Sillybutts/Alchemist/STLs Alchemist 3-7-2024/STLs1_Main/Green/Grip_Left.stl

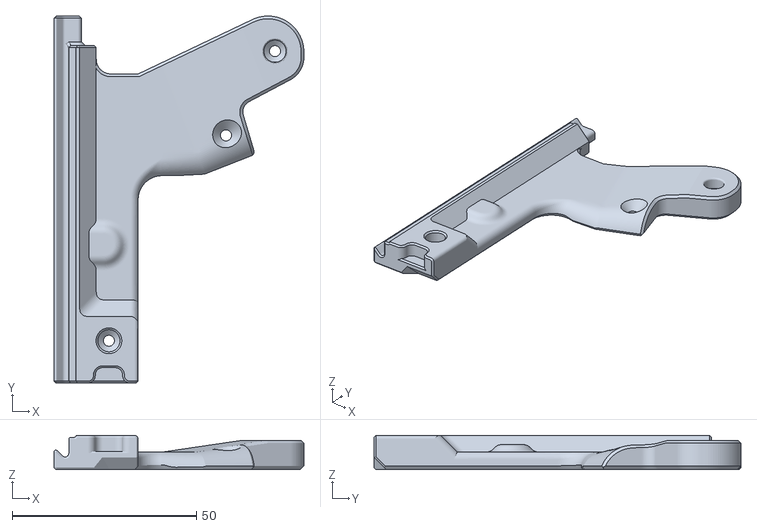
[picture p39: CAD file, 2024-03-08]
STLs Alchemist 3-7-2024/STLs1_Main/Green/Grip_Left.stl
67.8 x 99.5 x 9.25
