Sillybutts/Alchemist/STLs Alchemist 3-7-2024/STLs1_Main/Orange/Sear March2024Update.stl

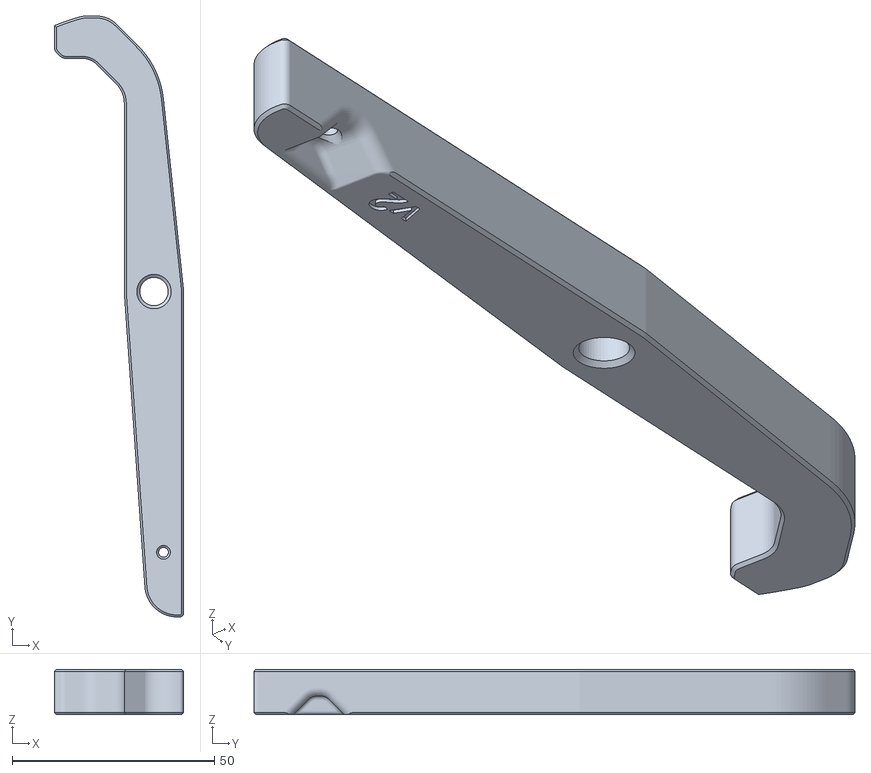
[picture p40: CAD file, 2024-03-08]
STLs Alchemist 3-7-2024/STLs1_Main/Orange/Sear March2024Update.stl
32.0 x 148.7 x 11.2
