Sillybutts/Alchemist/STLs Alchemist 3-7-2024/STLs1_Main/Stocks/Skeggox Stock/Skeggox_Bottom.stl

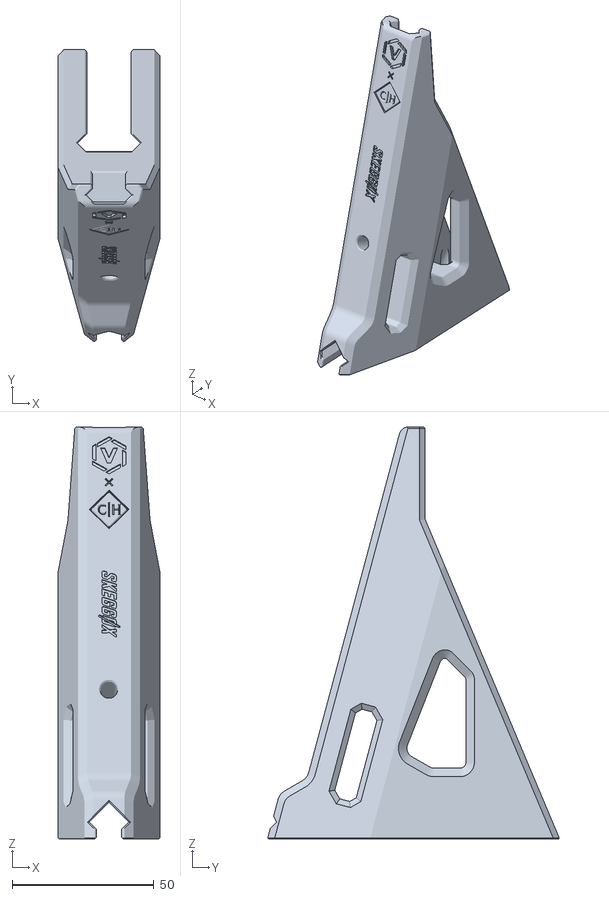
[picture p42: CAD file, 2024-03-08]
STLs Alchemist 3-7-2024/STLs1_Main/Stocks/Skeggox Stock/Skeggox_Bottom.stl
36.0 x 103.0 x 145.6
