Sillybutts/Alchemist/STLs Alchemist 3-7-2024/STLs1_Main/Stocks/Worker-SBL Stock/SBLWRKRSTOCK_Latch.stl

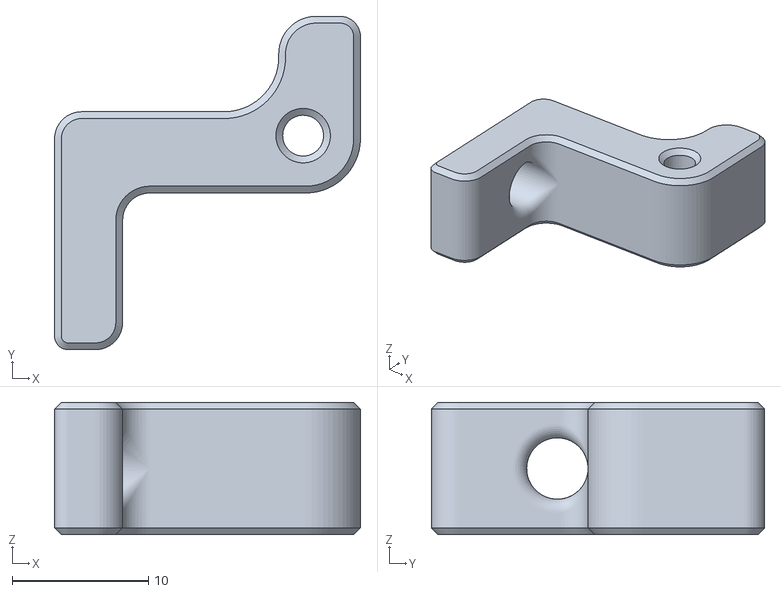
[picture p43: CAD file, 2023-09-10]
STLs Alchemist 3-7-2024/STLs1_Main/Stocks/Worker-SBL Stock/SBLWRKRSTOCK_Latch.stl
22.4 x 24.5 x 9.70
