Sillybutts/Alchemist/STLs Alchemist 3-7-2024/STLs2_Extras/Extras/Lynx Grip/Lynx_GripRight.stl

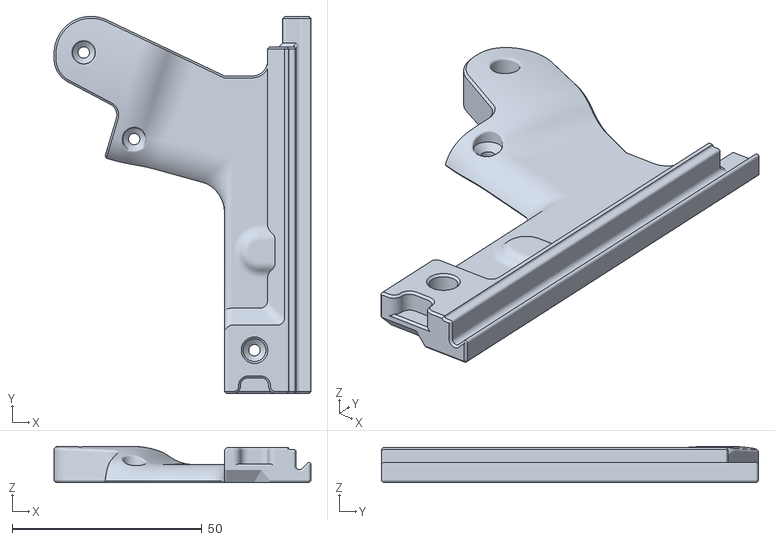
[picture p44: CAD file, 2024-03-08]
STLs Alchemist 3-7-2024/STLs2_Extras/Extras/Lynx Grip/Lynx_GripRight.stl
67.8 x 99.5 x 9.52
