Sillybutts/Alchemist/STLs Alchemist 3-7-2024/STLs2_Extras/Extras/SpigotSCAR/SpigotSCAR_BarrelCap.stl

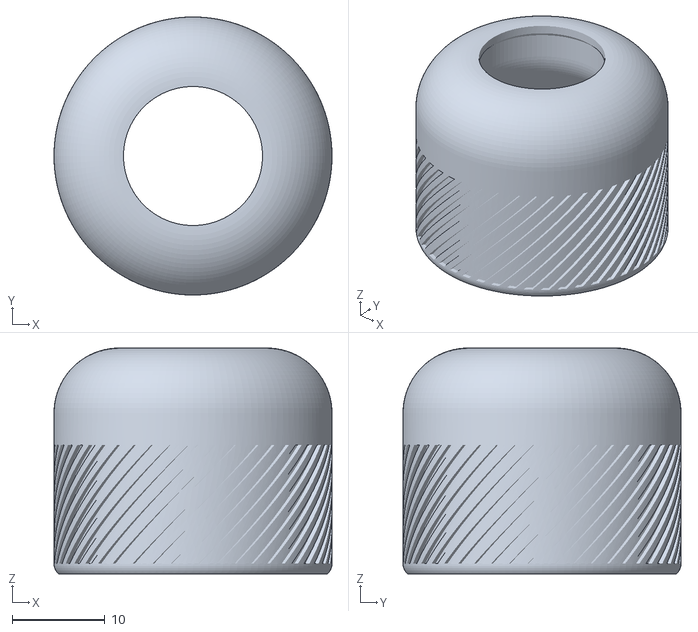
[picture p45: CAD file, 2023-09-10]
STLs Alchemist 3-7-2024/STLs2_Extras/Extras/SpigotSCAR/SpigotSCAR_BarrelCap.stl
30.0 x 30.0 x 24.4
