Sillybutts/Alchemist/STLs Alchemist 3-7-2024/STLs1_Main/Black/Alternate plunger rods/PlungerRod_TroubleshootingFix March2024Update.stl

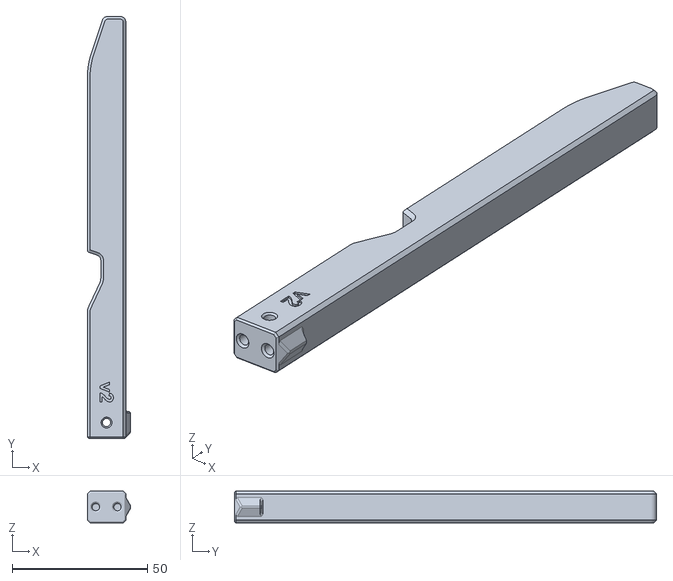
[picture p46: CAD file, 2024-03-08]
STLs Alchemist 3-7-2024/STLs1_Main/Black/Alternate plunger rods/PlungerRod_TroubleshootingFix March2024Update.stl
16.1 x 156.2 x 11.7
