Sillybutts/Alchemist/STLs Alchemist 3-7-2024/STLs1_Main/Black/Rail_C_Smooth.stl

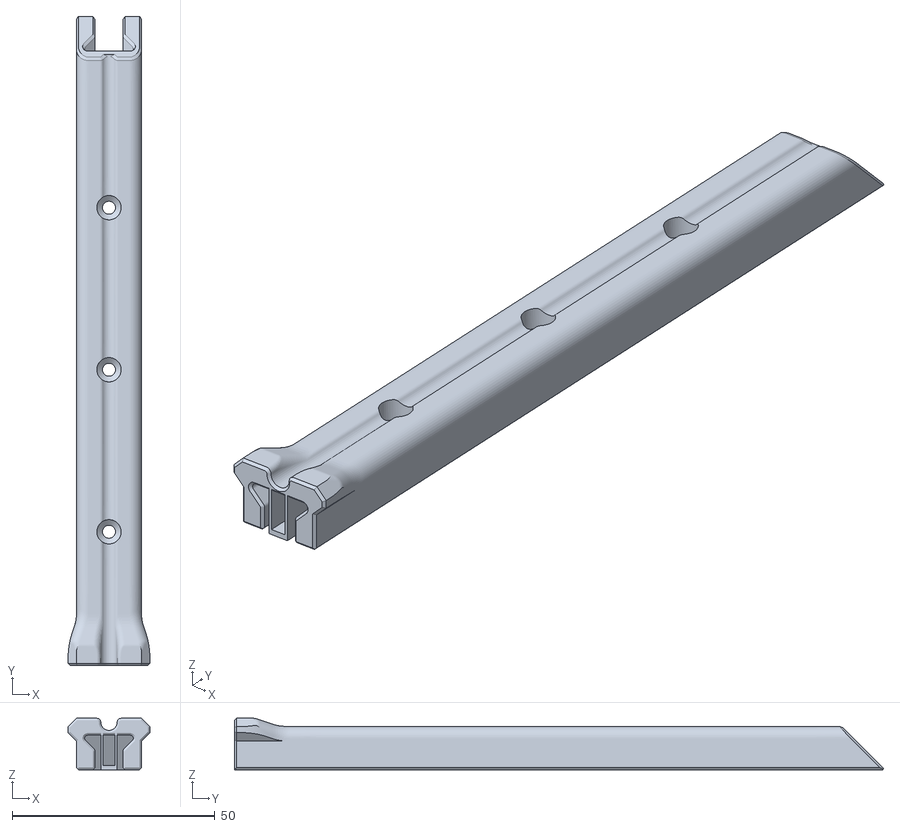
[picture p47: CAD file, 2024-03-08]
STLs Alchemist 3-7-2024/STLs1_Main/Black/Rail_C_Smooth.stl
20.2 x 160.2 x 12.7
