Sillybutts/Alchemist/STLs Alchemist 3-7-2024/STLs1_Main/Orange/PicKeeperTighter.stl

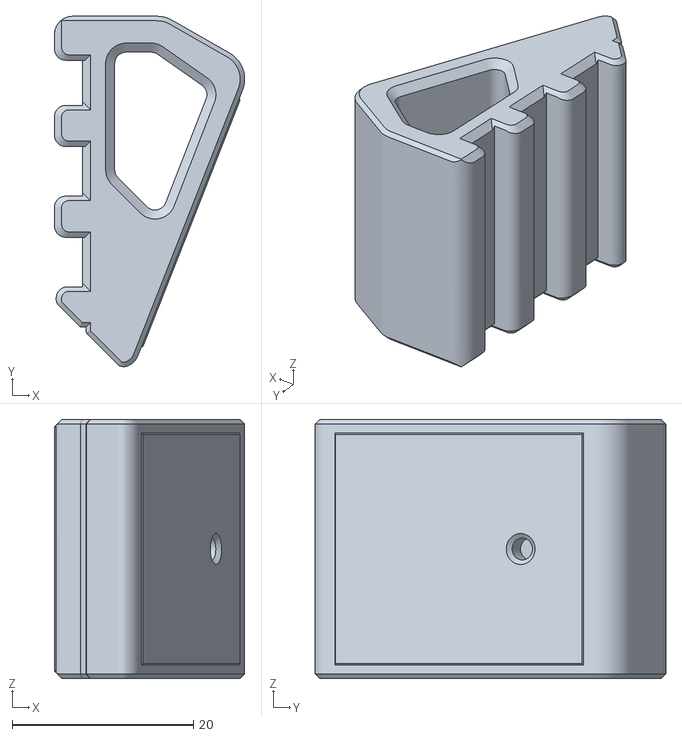
[picture p48: CAD file, 2024-03-08]
STLs Alchemist 3-7-2024/STLs1_Main/Orange/PicKeeperTighter.stl
21.0 x 38.7 x 28.6
