Sillybutts/Alchemist/STLs Alchemist 3-7-2024/STLs1_Main/Stocks/Fixed Stock/FixedStock_Stock.stl

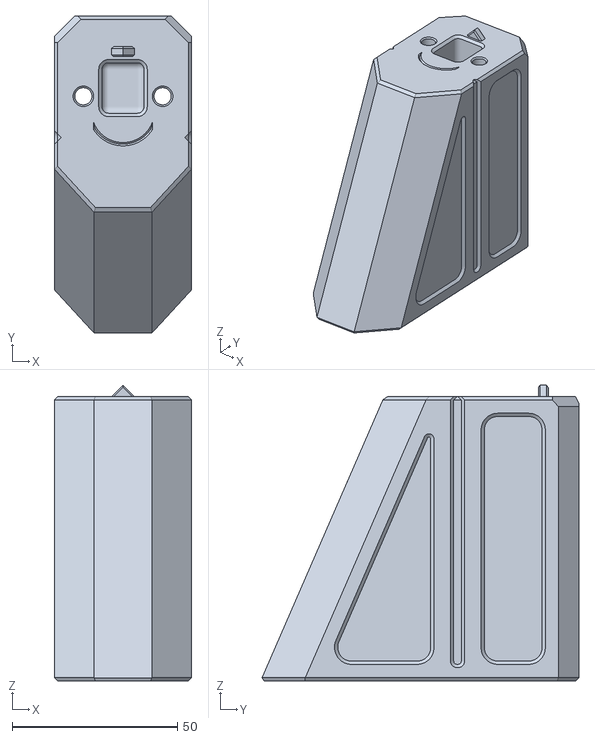
[picture p49: CAD file, 2023-09-10]
STLs Alchemist 3-7-2024/STLs1_Main/Stocks/Fixed Stock/FixedStock_Stock.stl
41.6 x 96.0 x 89.5
