Sillybutts/Alchemist/STLs Alchemist 3-7-2024/STLs1_Main/Stocks/Worker-SBL Stock/SBL_Buttplate.stl

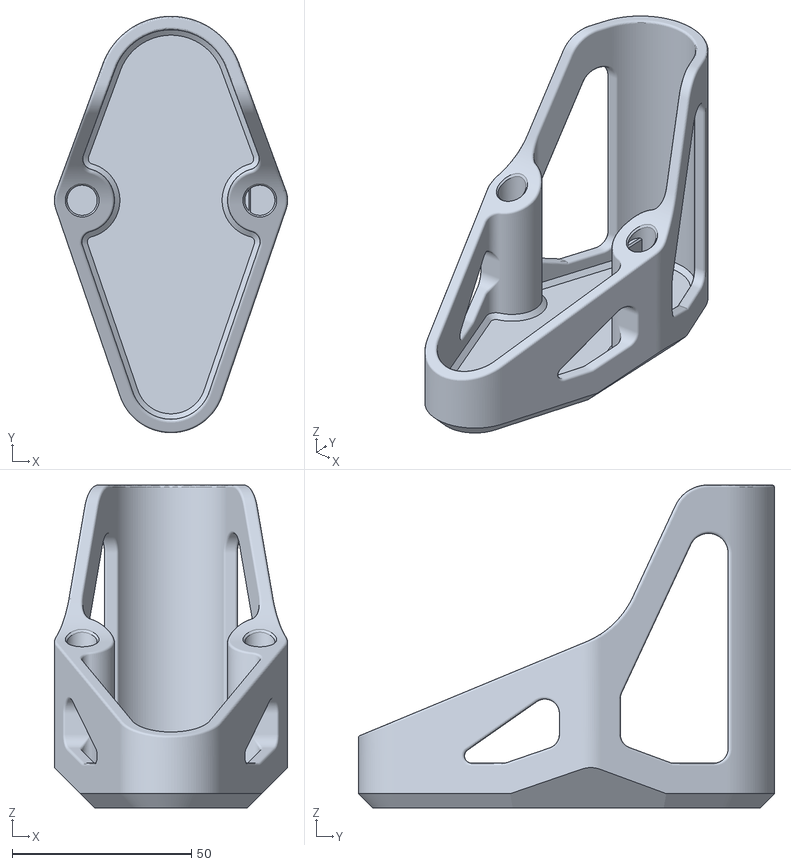
[picture p51: CAD file, 2023-09-10]
STLs Alchemist 3-7-2024/STLs1_Main/Stocks/Worker-SBL Stock/SBL_Buttplate.stl
65.0 x 116.0 x 90.0
