Sillybutts/Alchemist/STLs Alchemist 3-7-2024/STLs2_Extras/Extras/Lynx Grip/Lynx_GripBody_WithShoe.stl

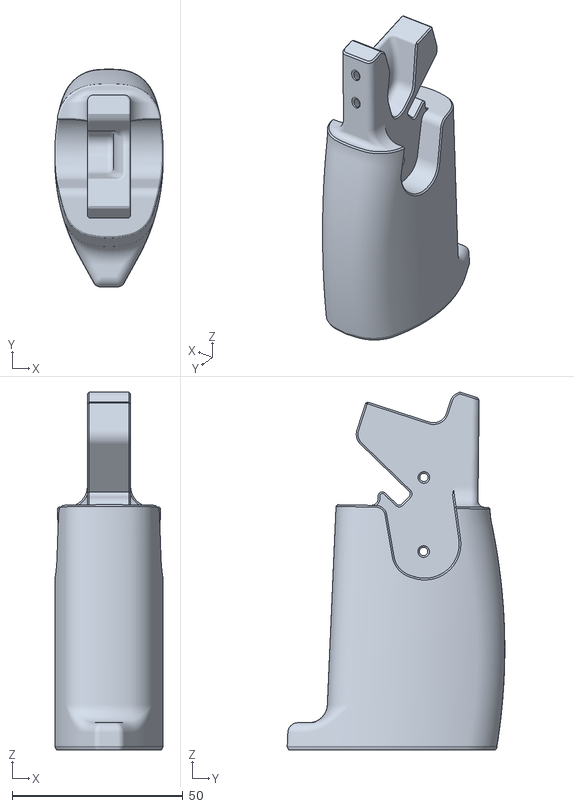
[picture p52: CAD file, 2024-03-08]
STLs Alchemist 3-7-2024/STLs2_Extras/Extras/Lynx Grip/Lynx_GripBody_WithShoe.stl
31.7 x 63.8 x 104.9
