Sillybutts/Alchemist/STLs Alchemist 3-7-2024/STLs2_Extras/Extras/Mag Release with more Trigger Guard space/SmallerArm_MagRelease.stl

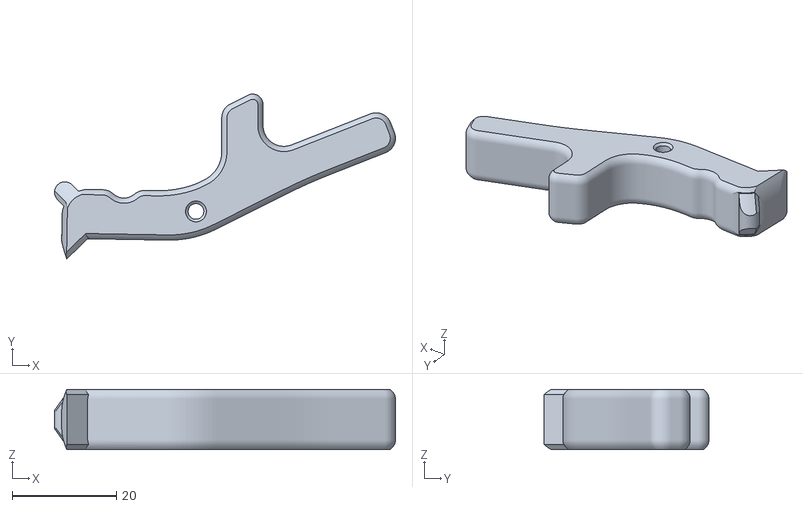
[picture p53: CAD file, 2023-09-10]
STLs Alchemist 3-7-2024/STLs2_Extras/Extras/Mag Release with more Trigger Guard space/SmallerArm_MagRelease.stl
65.4 x 31.6 x 11.5
