Sillybutts/Alchemist/STLs Alchemist 3-7-2024/STLs2_Extras/Extras/PicKeeper original looseness parts/original FrontGrip.stl

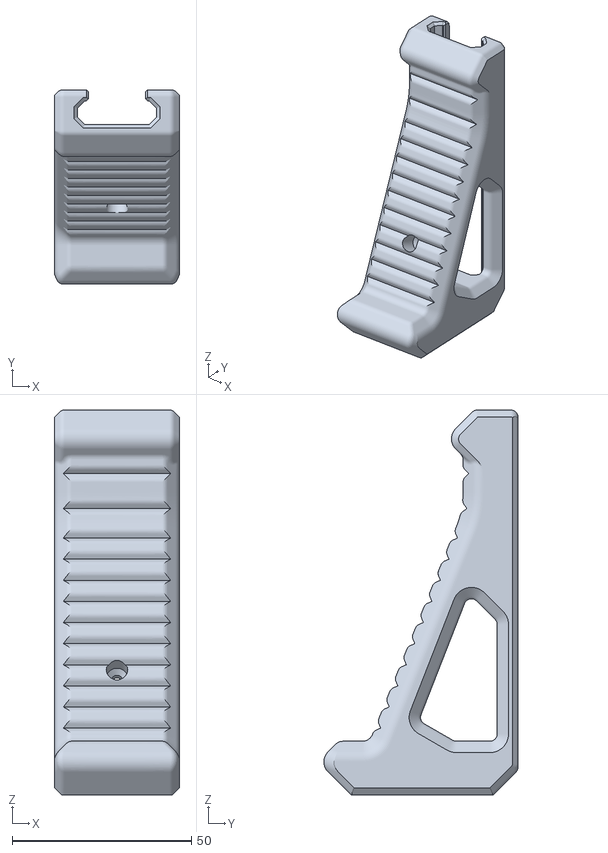
[picture p54: CAD file, 2024-03-08]
STLs Alchemist 3-7-2024/STLs2_Extras/Extras/PicKeeper original looseness parts/original FrontGrip.stl
34.9 x 54.2 x 107.4
