Sillybutts/Alchemist/STLs Alchemist 3-7-2024/STLs2_Extras/Extras/Tools/PT length gauge.stl

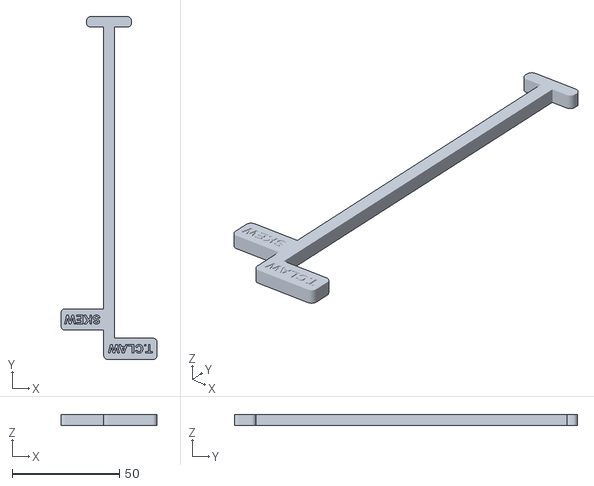
[picture p55: CAD file, 2023-09-10]
STLs Alchemist 3-7-2024/STLs2_Extras/Extras/Tools/PT length gauge.stl
45.0 x 160.3 x 5.00
