Sillybutts/Alchemist/STLs Alchemist 3-7-2024/STLs1_Main/Black/Rail_A.stl

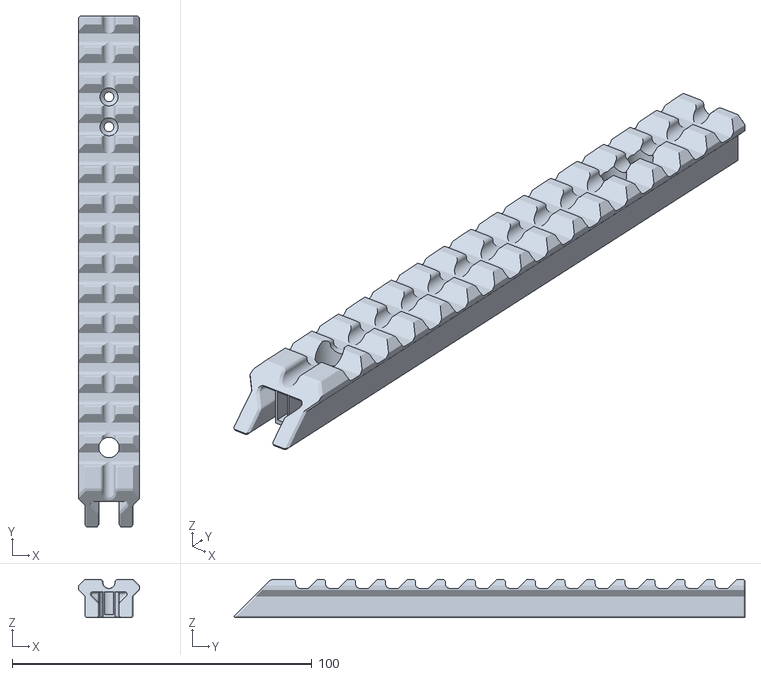
[picture p56: CAD file, 2024-03-08]
STLs Alchemist 3-7-2024/STLs1_Main/Black/Rail_A.stl
20.2 x 170.6 x 12.7
