Sillybutts/Alchemist/STLs Alchemist 3-7-2024/STLs1_Main/Green/MagwellBack.stl

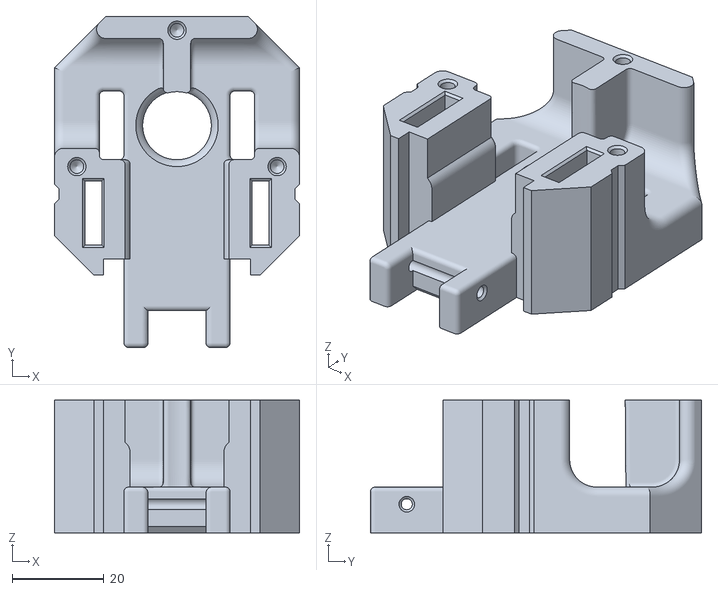
[picture p57: CAD file, 2024-03-08]
STLs Alchemist 3-7-2024/STLs1_Main/Green/MagwellBack.stl
53.6 x 72.3 x 29.0
