Sillybutts/Alchemist/STLs Alchemist 3-7-2024/STLs1_Main/Stocks/Worker-SBL Stock/SBLWRKRSTOCK_EndCapB.stl

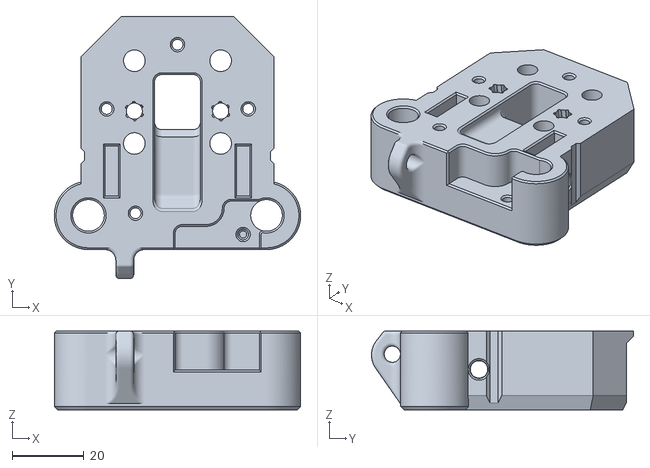
[picture p59: CAD file, 2023-09-10]
STLs Alchemist 3-7-2024/STLs1_Main/Stocks/Worker-SBL Stock/SBLWRKRSTOCK_EndCapB.stl
68.5 x 72.8 x 21.9
