Sillybutts/Alchemist/STLs Alchemist 3-7-2024/STLs1_Main/Green/DetentBlock.stl

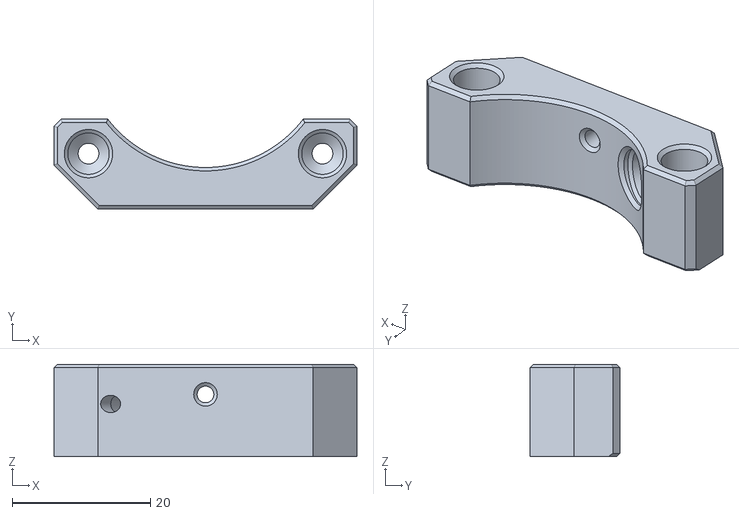
[picture p61: CAD file, 2024-03-08]
STLs Alchemist 3-7-2024/STLs1_Main/Green/DetentBlock.stl
43.9 x 13.0 x 13.4
