Sillybutts/Alchemist/STLs Alchemist 3-7-2024/STLs1_Main/Orange/PlungerHead_B.stl

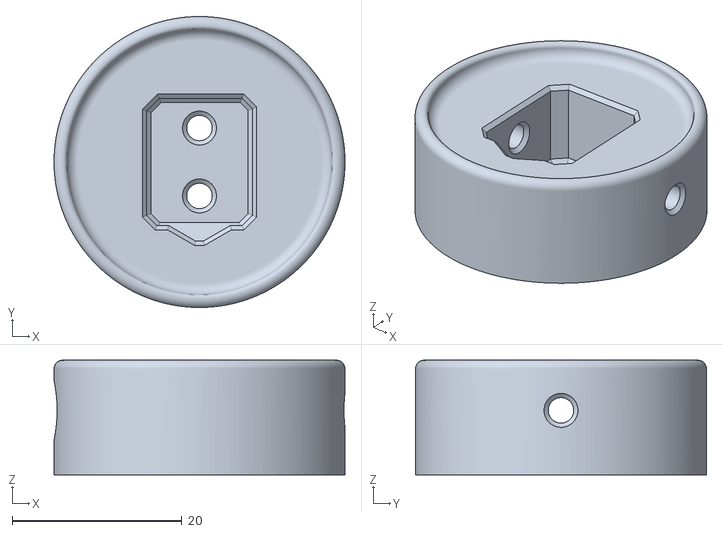
[picture p62: CAD file, 2024-03-08]
STLs Alchemist 3-7-2024/STLs1_Main/Orange/PlungerHead_B.stl
34.3 x 34.3 x 13.5
