Sillybutts/Alchemist/STLs Alchemist 3-7-2024/STLs1_Main/Stocks/Fixed Stock/FixedStock_Buttplate_10mm.stl

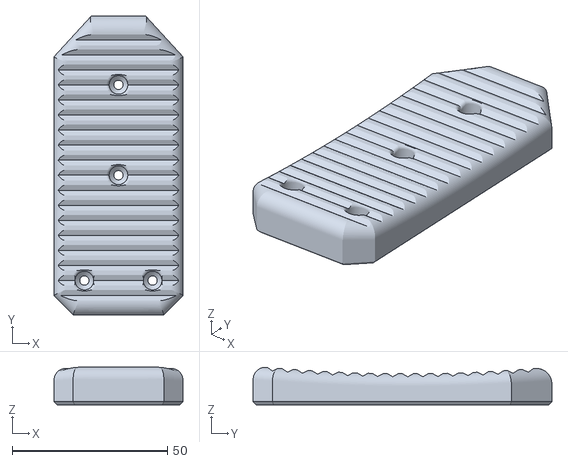
[picture p63: CAD file, 2023-09-10]
STLs Alchemist 3-7-2024/STLs1_Main/Stocks/Fixed Stock/FixedStock_Buttplate_10mm.stl
41.6 x 96.4 x 12.1
