Sillybutts/Alchemist/STLs Alchemist 3-7-2024/STLs1_Main/Stocks/Worker-SBL Stock/SBLWRKRSTOCK_CoverTube.stl

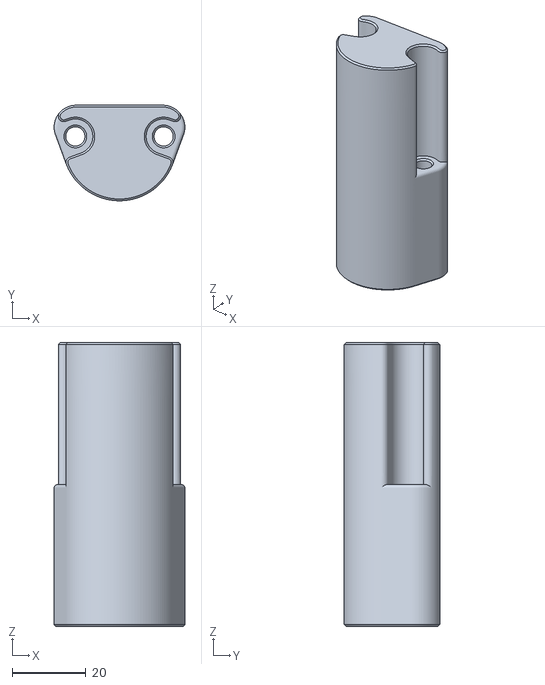
[picture p64: CAD file, 2023-09-10]
STLs Alchemist 3-7-2024/STLs1_Main/Stocks/Worker-SBL Stock/SBLWRKRSTOCK_CoverTube.stl
35.6 x 26.0 x 77.2
