Sillybutts/Alchemist/STLs Alchemist 3-7-2024/STLs2_Extras/Extras/Lynx Grip/Lynx_GripBeavertail.stl

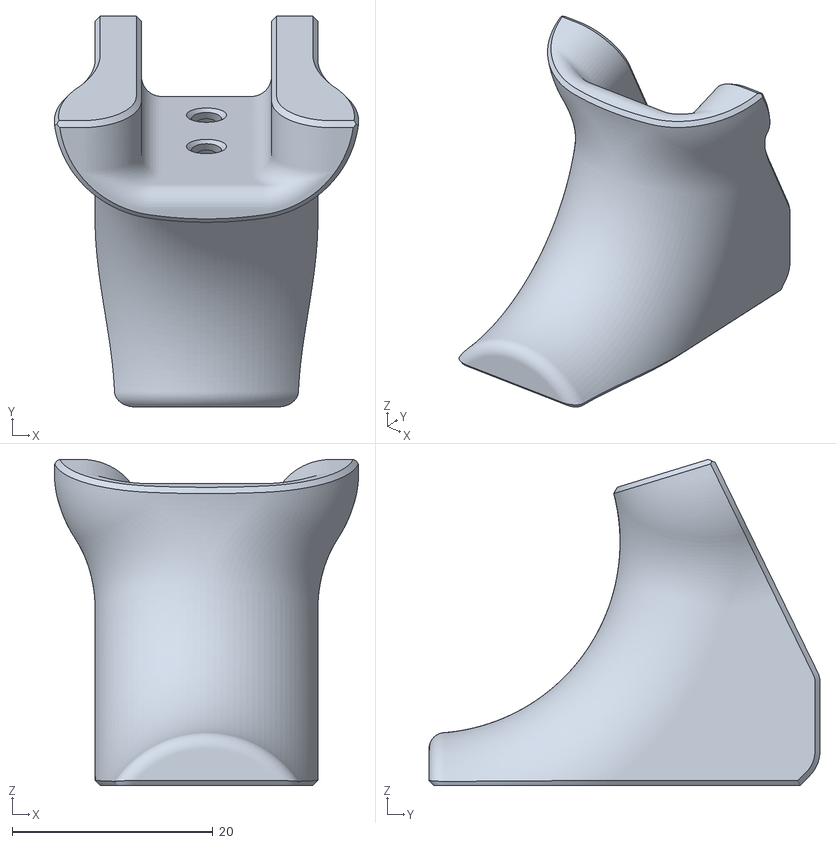
[picture p65: CAD file, 2023-09-10]
STLs Alchemist 3-7-2024/STLs2_Extras/Extras/Lynx Grip/Lynx_GripBeavertail.stl
30.4 x 39.0 x 32.5
