Sillybutts/Alchemist/STLs Alchemist 3-7-2024/STLs1_Main/Green/Magwell_Right_NoWindows.stl

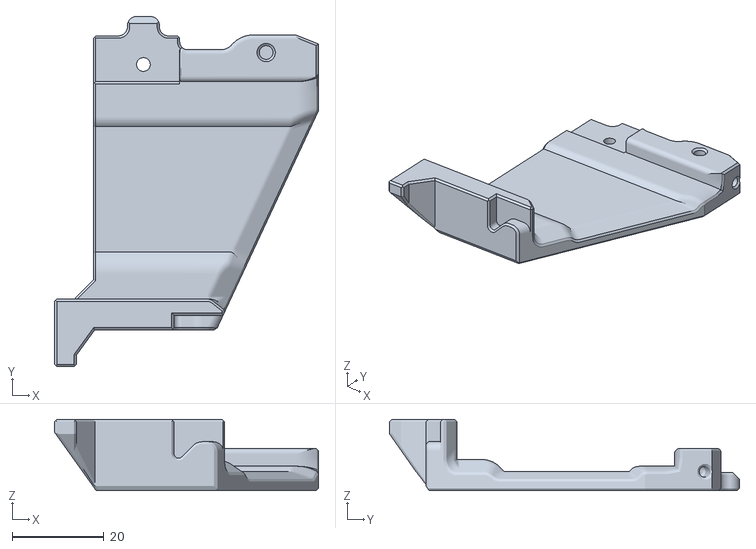
[picture p66: CAD file, 2023-10-14]
STLs Alchemist 3-7-2024/STLs1_Main/Green/Magwell_Right_NoWindows.stl
57.7 x 76.5 x 15.6
