Sillybutts/Alchemist/STLs Alchemist 3-7-2024/STLs1_Main/Orange/PlungerHead_A.stl

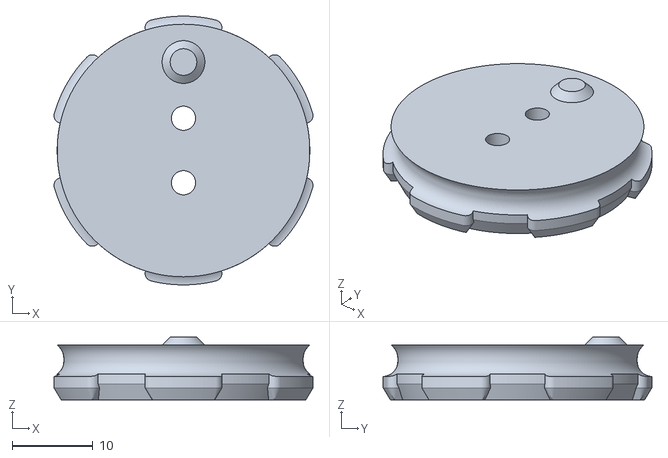
[picture p67: CAD file, 2024-03-08]
STLs Alchemist 3-7-2024/STLs1_Main/Orange/PlungerHead_A.stl
32.1 x 33.3 x 7.80
