Sillybutts/Alchemist/STLs Alchemist 3-7-2024/STLs1_Main/Stocks/Fixed Stock/FixedStock_Buttplate_20mm.stl

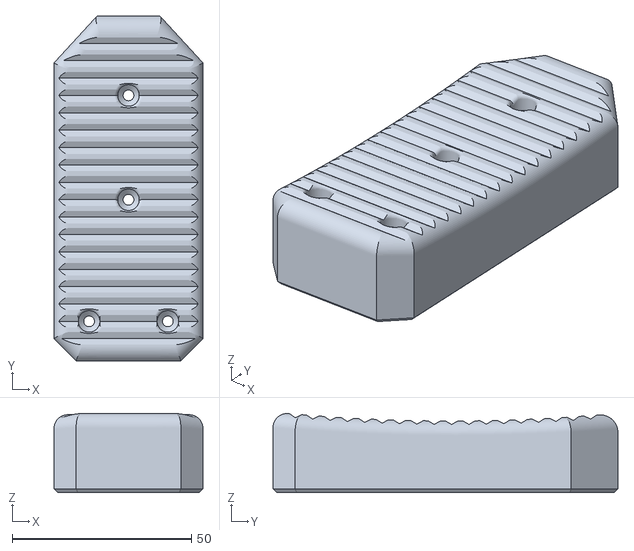
[picture p68: CAD file, 2023-09-10]
STLs Alchemist 3-7-2024/STLs1_Main/Stocks/Fixed Stock/FixedStock_Buttplate_20mm.stl
41.6 x 96.4 x 22.1
