Sillybutts/Alchemist/STLs Alchemist 3-7-2024/STLs1_Main/Stocks/Skeggox Stock/Skeggox_Top.stl

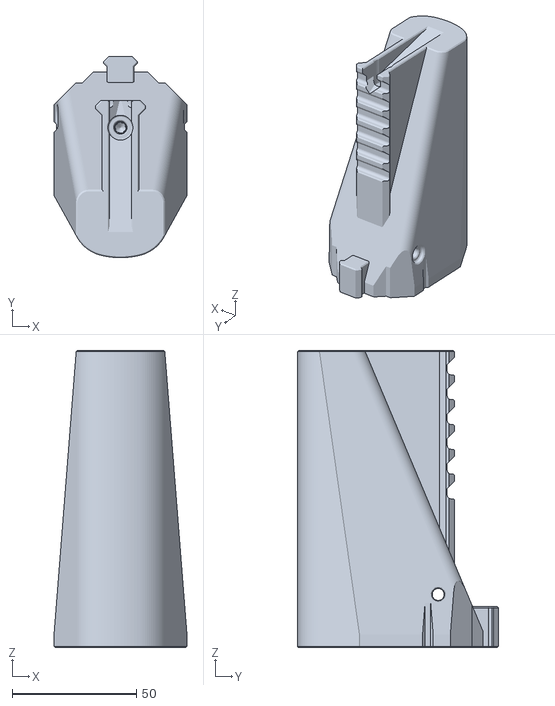
[picture p69: CAD file, 2024-03-08]
STLs Alchemist 3-7-2024/STLs1_Main/Stocks/Skeggox Stock/Skeggox_Top.stl
53.6 x 81.1 x 119.7
