Sillybutts/Alchemist/STLs Alchemist 3-7-2024/STLs2_Extras/Extras/Lynx Grip/Lynx_TriggerGuard.stl

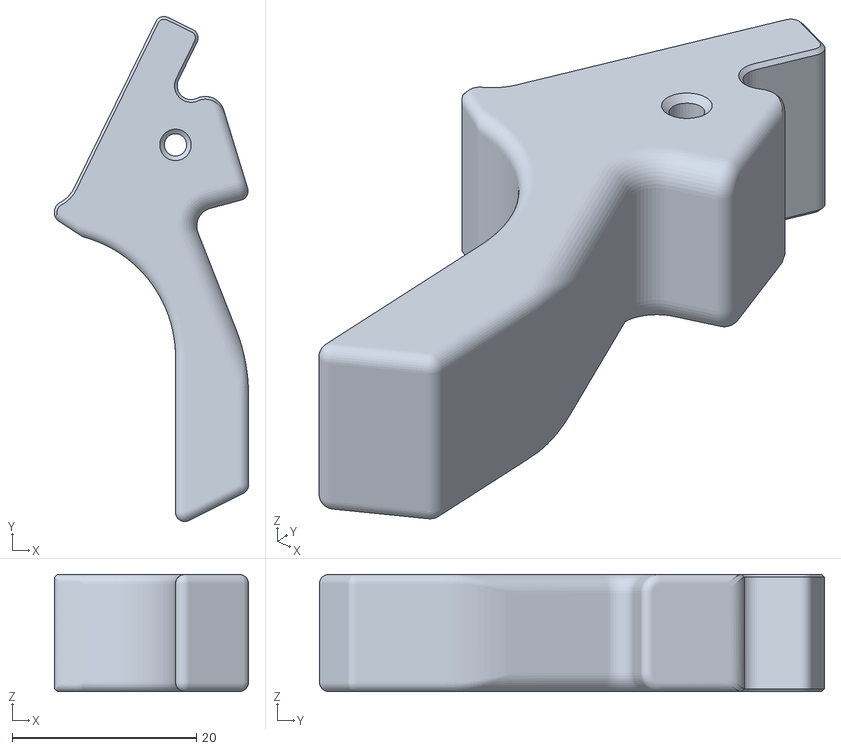
[picture p70: CAD file, 2023-09-10]
STLs Alchemist 3-7-2024/STLs2_Extras/Extras/Lynx Grip/Lynx_TriggerGuard.stl
21.1 x 54.8 x 12.7
