Sillybutts/Alchemist/STLs Alchemist 3-7-2024/STLs1_Main/Orange/MuzzleNut.stl

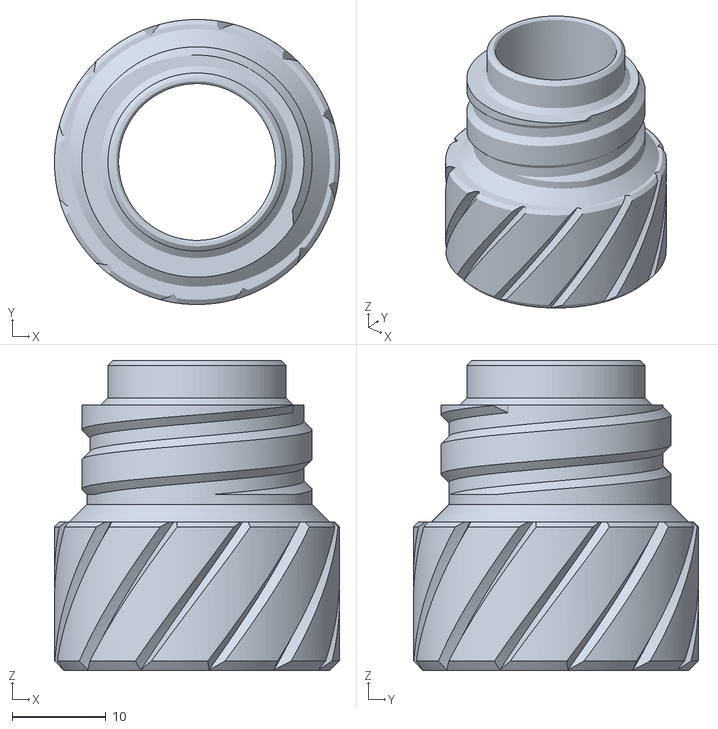
[picture p71: CAD file, 2023-09-10]
STLs Alchemist 3-7-2024/STLs1_Main/Orange/MuzzleNut.stl
30.5 x 30.5 x 33.1
