Sillybutts/Alchemist/STLs Alchemist 3-7-2024/STLs1_Main/Stocks/Skeggox Stock/Skeggox_Buttplate_VERTICALPRINT.stl

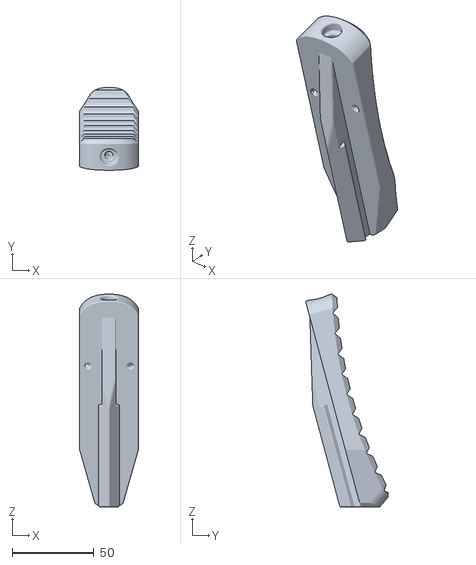
[picture p72: CAD file, 2023-09-10]
STLs Alchemist 3-7-2024/STLs1_Main/Stocks/Skeggox Stock/Skeggox_Buttplate_VERTICALPRINT.stl
36.0 x 50.6 x 130.5
