Sillybutts/Alchemist/STLs Alchemist 3-7-2024/STLs1_Main/Black/GripBody_NoShoe.stl

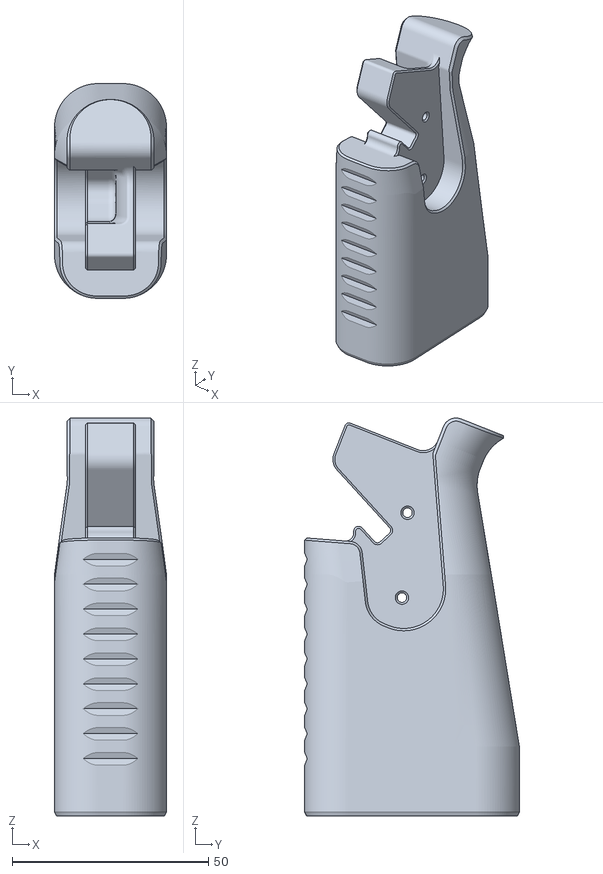
[picture p73: CAD file, 2024-03-08]
STLs Alchemist 3-7-2024/STLs1_Main/Black/GripBody_NoShoe.stl
28.6 x 54.8 x 101.5
