Sillybutts/Alchemist/STLs Alchemist 3-7-2024/STLs1_Main/Green/BarrelShroudBack.stl

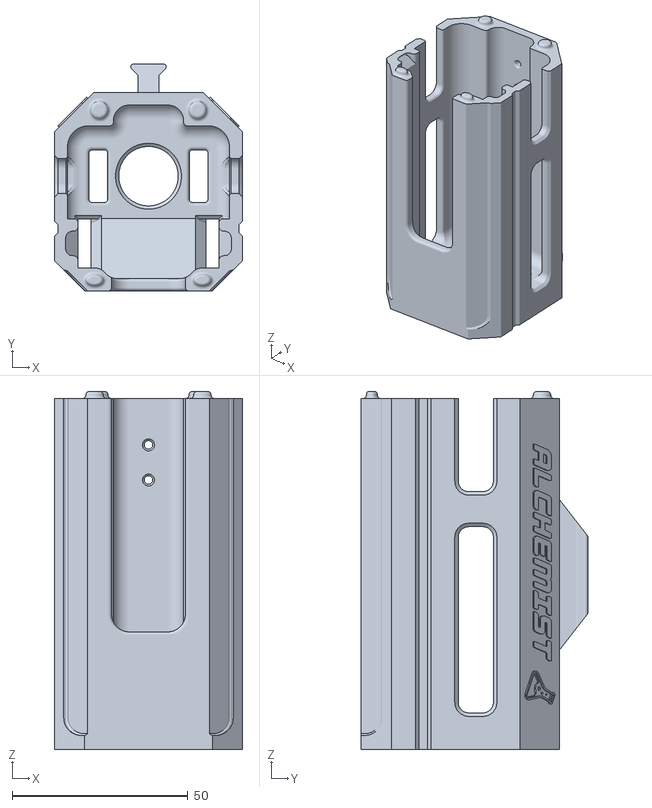
[picture p74: CAD file, 2023-09-10]
STLs Alchemist 3-7-2024/STLs1_Main/Green/BarrelShroudBack.stl
53.6 x 64.6 x 101.9
