Sillybutts/Alchemist/STLs Alchemist 3-7-2024/STLs1_Main/Orange/BarTensioningBlock.stl

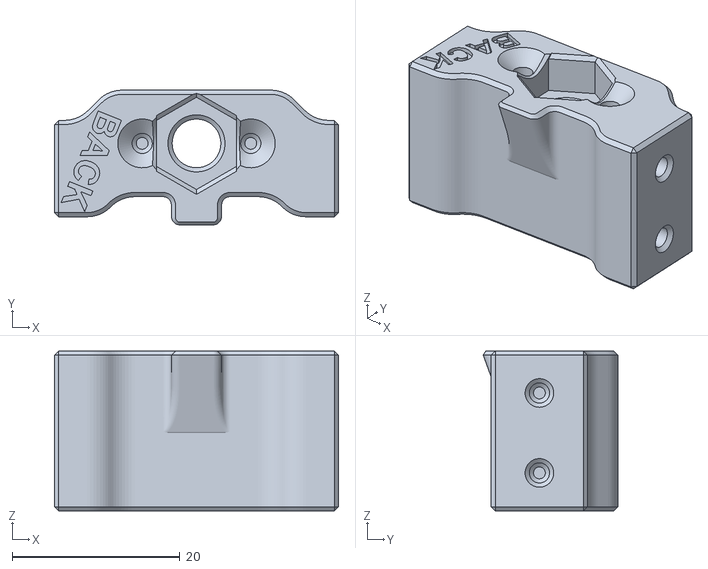
[picture p75: CAD file, 2023-09-10]
STLs Alchemist 3-7-2024/STLs1_Main/Orange/BarTensioningBlock.stl
33.9 x 16.1 x 19.1
