Sillybutts/Alchemist/STLs Alchemist 3-7-2024/STLs1_Main/Stocks/Skeggox Stock/Skeggox_Buttplate_HORIZONTALPRINT.stl

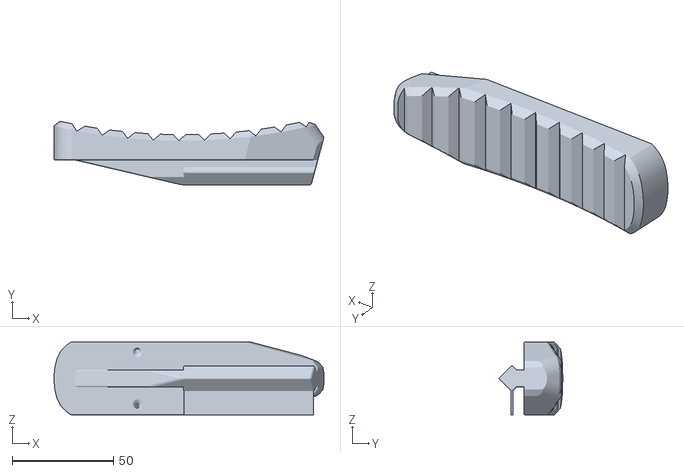
[picture p76: CAD file, 2023-09-10]
STLs Alchemist 3-7-2024/STLs1_Main/Stocks/Skeggox Stock/Skeggox_Buttplate_HORIZONTALPRINT.stl
133.6 x 31.4 x 36.0
