Sillybutts/Alchemist/STLs Alchemist 3-7-2024/STLs1_Main/Green/Magwell_Left.stl

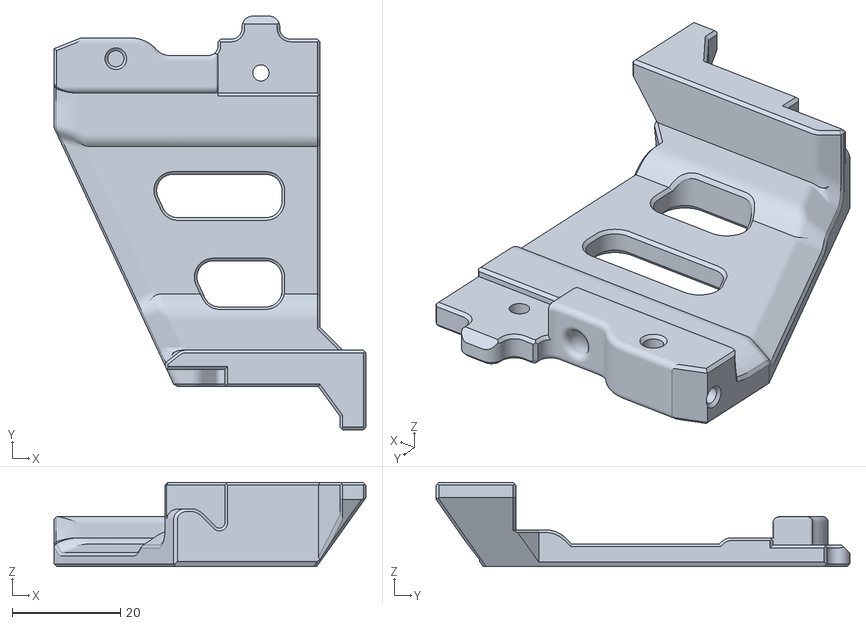
[picture p77: CAD file, 2023-09-10]
STLs Alchemist 3-7-2024/STLs1_Main/Green/Magwell_Left.stl
57.7 x 76.5 x 15.6
