Sillybutts/Alchemist/STLs Alchemist 3-7-2024/STLs1_Main/Orange/RamBaseBack.stl

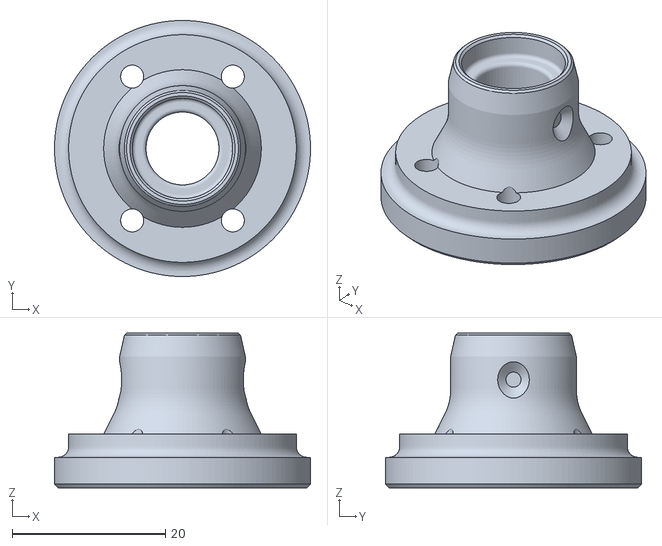
[picture p78: CAD file, 2023-09-10]
STLs Alchemist 3-7-2024/STLs1_Main/Orange/RamBaseBack.stl
33.4 x 33.4 x 20.2
