Sillybutts/Alchemist/STLs Alchemist 3-7-2024/STLs1_Main/Black/MagwellChin.stl

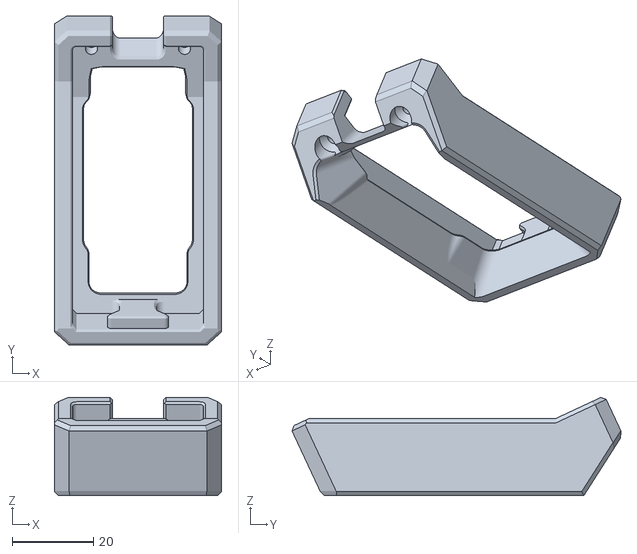
[picture p79: CAD file, 2023-09-10]
STLs Alchemist 3-7-2024/STLs1_Main/Black/MagwellChin.stl
41.2 x 81.1 x 24.2
