Sillybutts/Alchemist/STLs Alchemist 3-7-2024/STLs1_Main/Green/MagwellFront.stl

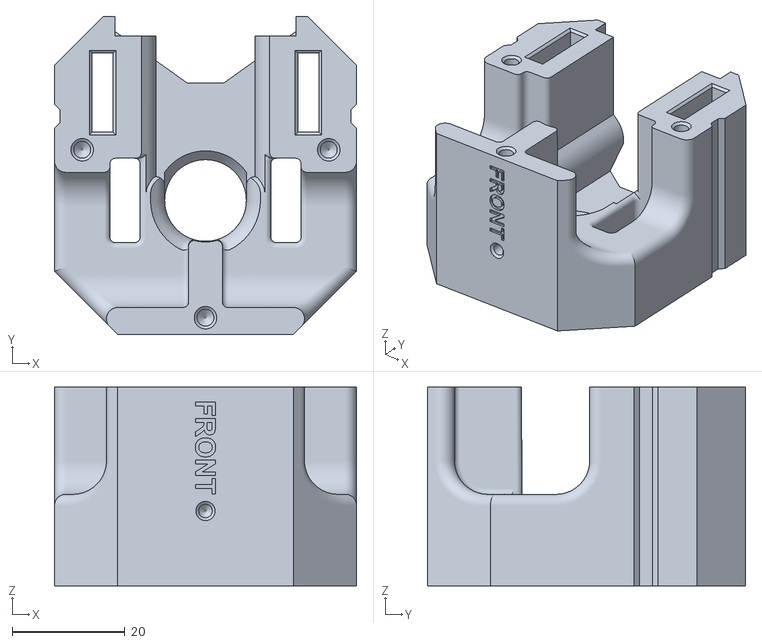
[picture p80: CAD file, 2023-09-10]
STLs Alchemist 3-7-2024/STLs1_Main/Green/MagwellFront.stl
53.6 x 56.5 x 35.2
