Sillybutts/Alchemist/STLs Alchemist 3-7-2024/STLs1_Main/Orange/Muzzle.stl

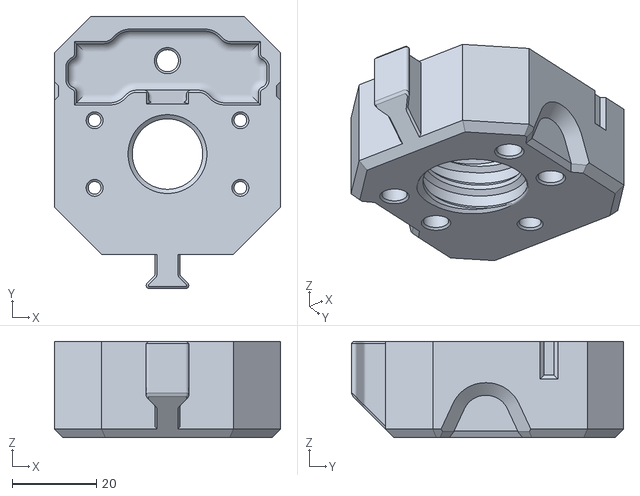
[picture p81: CAD file, 2023-09-10]
STLs Alchemist 3-7-2024/STLs1_Main/Orange/Muzzle.stl
53.6 x 64.6 x 22.8
