Sillybutts/Alchemist/STLs Alchemist 3-7-2024/STLs1_Main/Green/PTfront.stl

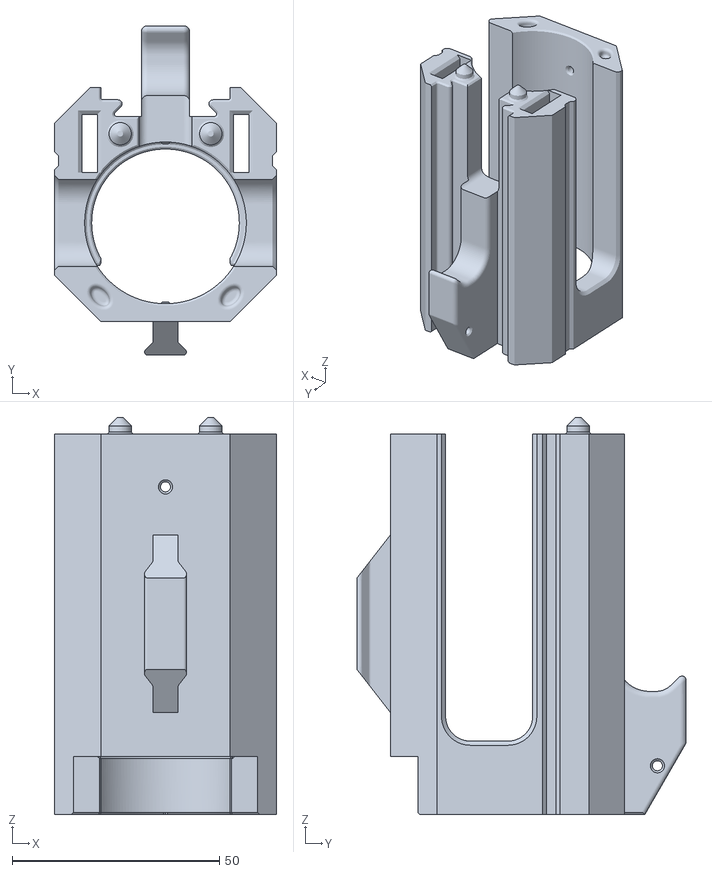
[picture p82: CAD file, 2023-09-10]
STLs Alchemist 3-7-2024/STLs1_Main/Green/PTfront.stl
53.6 x 79.5 x 95.8
