Sillybutts/Alchemist/STLs Alchemist 3-7-2024/STLs1_Main/Orange/PrimingBlock_BearingBumpers.stl

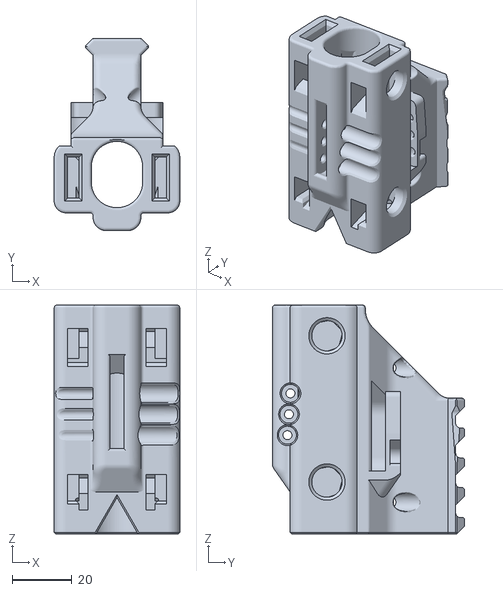
[picture p83: CAD file, 2023-09-10]
STLs Alchemist 3-7-2024/STLs1_Main/Orange/PrimingBlock_BearingBumpers.stl
42.1 x 64.4 x 76.7
