Sillybutts/Alchemist/STLs Alchemist 3-7-2024/STLs1_Main/Green/BarrelShroudFront.stl

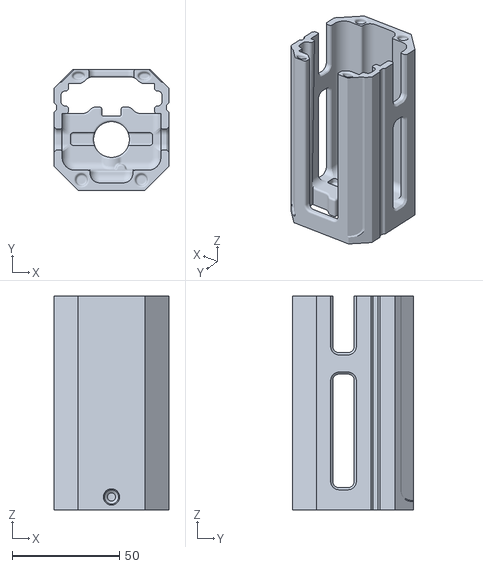
[picture p84: CAD file, 2023-09-10]
STLs Alchemist 3-7-2024/STLs1_Main/Green/BarrelShroudFront.stl
53.6 x 56.5 x 99.9
