Sillybutts/Alchemist/STLs Alchemist 3-7-2024/STLs1_Main/Orange/MagRelease.stl

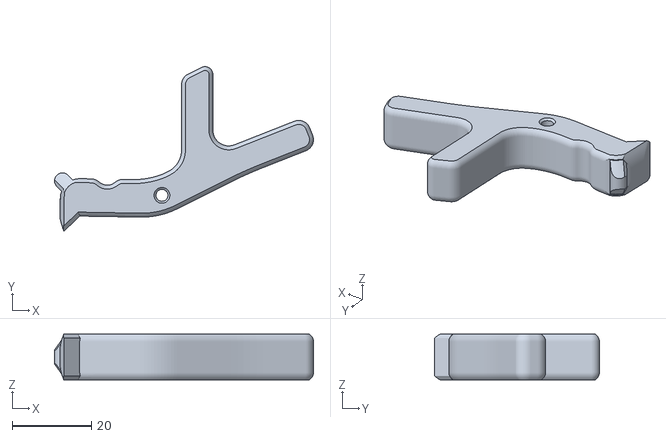
[picture p85: CAD file, 2023-09-10]
STLs Alchemist 3-7-2024/STLs1_Main/Orange/MagRelease.stl
65.4 x 41.6 x 11.5
