Sillybutts/Alchemist/STLs Alchemist 3-7-2024/STLs1_Main/Orange/MuzzleNutThin.stl

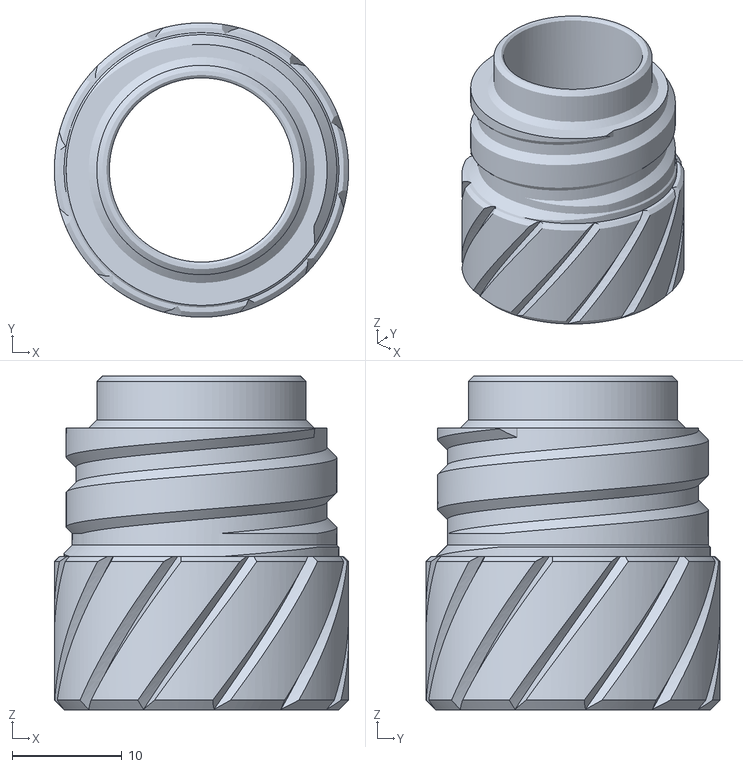
[picture p86: CAD file, 2023-09-10]
STLs Alchemist 3-7-2024/STLs1_Main/Orange/MuzzleNutThin.stl
26.8 x 26.8 x 30.4
