Sillybutts/Alchemist/STLs Alchemist 3-7-2024/STLs1_Main/Green/EndCap_Beaker.stl

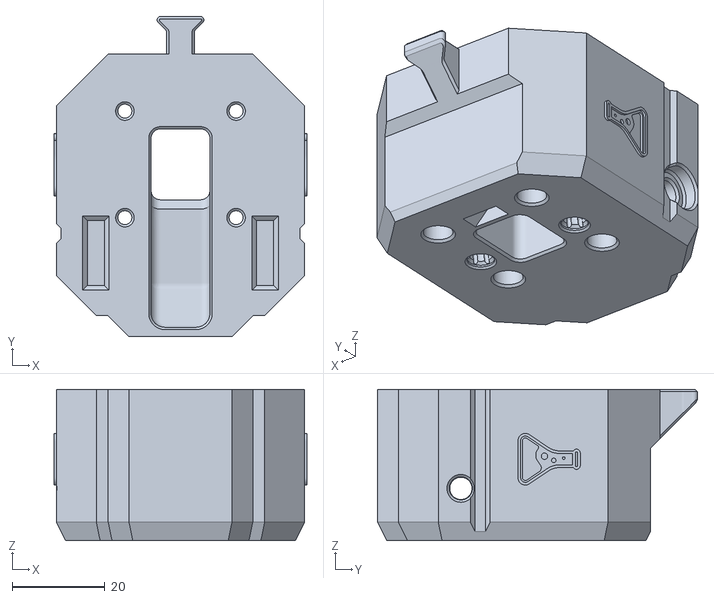
[picture p87: CAD file, 2023-09-10]
STLs Alchemist 3-7-2024/STLs1_Main/Green/EndCap_Beaker.stl
54.6 x 69.1 x 32.6
