Sillybutts/Alchemist/STLs Alchemist 3-7-2024/STLs1_Main/Orange/RamBaseFront.stl

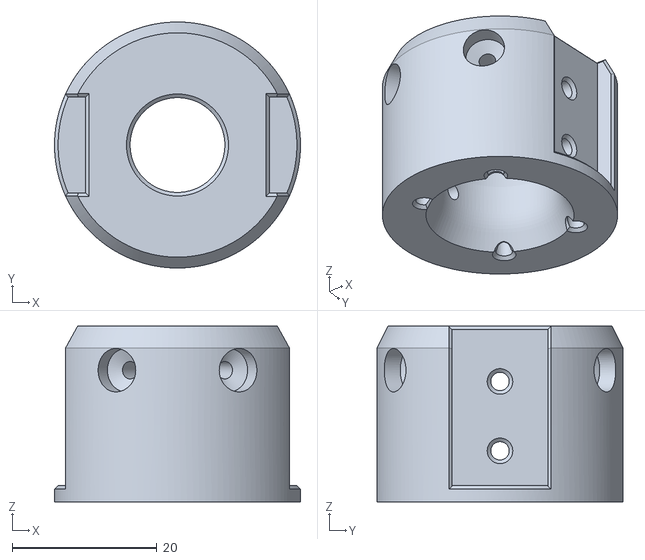
[picture p88: CAD file, 2023-09-10]
STLs Alchemist 3-7-2024/STLs1_Main/Orange/RamBaseFront.stl
34.0 x 34.0 x 24.3
