Sillybutts/Alchemist/STLs Alchemist 3-7-2024/STLs1_Main/Green/SearBlock.stl

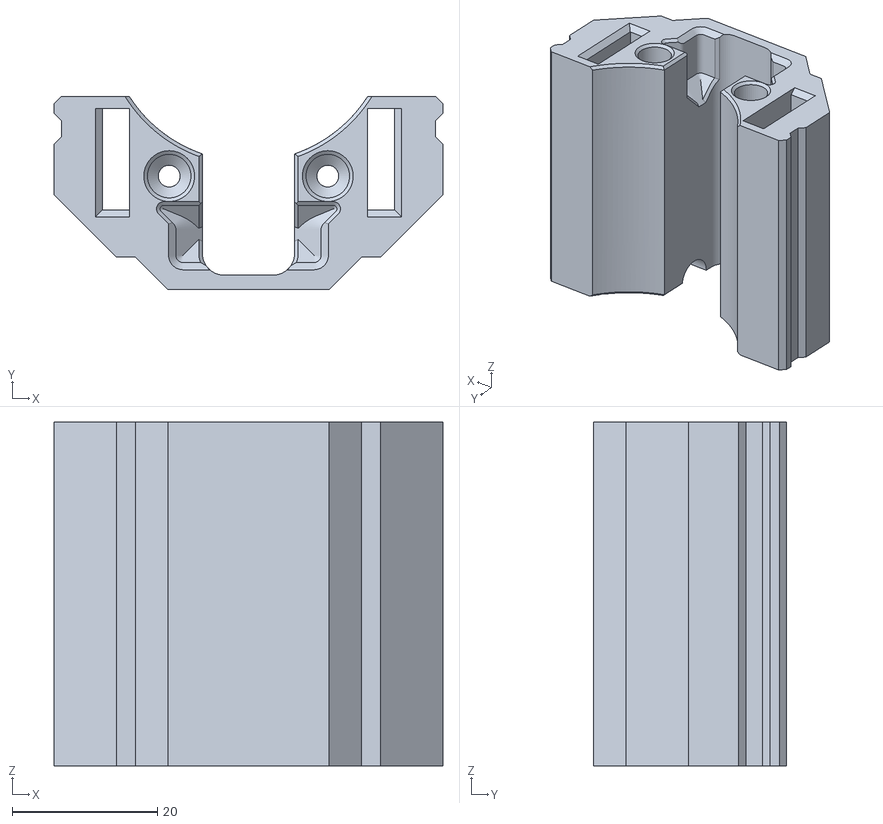
[picture p91: CAD file, 2023-09-10]
STLs Alchemist 3-7-2024/STLs1_Main/Green/SearBlock.stl
53.6 x 26.7 x 47.4
